slu4coder/Minimal-64x4-Home-Computer/Revision 1.4 Redux/Programs/asm/birds.asm

#org 0x8000       MIV pic,2 MIV 0x430c,4                  ; use zero-page pointers for source and target
                  MIZ 240,1                               ; number of lines to copy
  yloop:          MIZ 50,0                                ; bytes per line
  xloop:          MTT 2,4 INV 2 INV 4 DEZ 0 BGT xloop     ; transfer a line
                    AIV 14,4 DEZ 1 BGT yloop              ; advance to start of next line
                      JPS 0xf015                          ; API _WaitInput
                      JPA 0xf003                          ; API _Prompt
pic:                                                      ; 240 lines x 50 bytes per line
0x00,0x00,0x00,0x08,0x1b,0x00,0x00,0x00,0x00,0x00,0x00,0x00,0x00,0x00,0xc0,0xfd,0xff,0xff,0xff,0x7f,0x22,0x00,0x00,0x00,0x00,0x30,0x19,0x00,0x00,0x00,0x00,0x00,0x00,0x40,0x95,0x24,0x01,0x00,0x00,0x00,0x00,0x00,0x00,0x00,0x00,0x00,0x00,0x00,0x00,0x00,
0x00,0x40,0x24,0x82,0x33,0x49,0x15,0x00,0x00,0x00,0x00,0x00,0x00,0x80,0x60,0x93,0x2f,0xff,0x7f,0x2b,0x11,0x24,0x01,0x00,0x00,0x98,0x28,0x00,0x00,0x00,0x00,0x00,0x02,0xc0,0x76,0x2b,0x4a,0x02,0x00,0x00,0x00,0x00,0x00,0x00,0x00,0x00,0x40,0x12,0x01,0x00,
0x00,0x80,0x10,0x94,0x29,0x22,0x48,0x14,0x00,0x00,0x00,0x00,0x00,0x00,0xa0,0xee,0xba,0xed,0xed,0x97,0x44,0x24,0x12,0x00,0x00,0x84,0x18,0x00,0x00,0x00,0x00,0x90,0x00,0x80,0xab,0x54,0x11,0xa4,0x24,0x09,0x00,0x00,0x00,0x00,0x50,0x2b,0x09,0x80,0x48,0x92,
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
0x00,0x93,0x20,0x7a,0x40,0x09,0x7e,0xc0,0x48,0xa9,0xeb,0x7e,0x00,0x00,0x00,0x00,0x80,0x10,0xf2,0xad,0xda,0x2b,0x3a,0x44,0x04,0x00,0x6f,0x05,0x80,0x69,0x65,0x2a,0xa4,0x80,0x0d,0x00,0x00,0xfe,0xff,0xff,0x00,0x04,0x09,0x00,0x00,0x02,0x00,0x00,0x02,0x00,
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
